drcrane/ledclock/esp8266terminal/londontzstruct.c

#include "tzstruct.h"

struct timezonechanges timezonechanges[] = 
{
{ 1521939600, 1540688400 }, // 2018
{ 1553994000, 1572138000 }, // 2019
{ 1585443600, 1603587600 }, // 2020
{ 1616893200, 1635642000 }, // 2021
{ 1648342800, 1667091600 }, // 2022
{ 1679792400, 1698541200 }, // 2023
{ 1711846800, 1729990800 }, // 2024
{ 1743296400, 1761440400 }, // 2025
{ 1774746000, 1792890000 }, // 2026
{ 1806195600, 1824944400 }, // 2027
{ 1837645200, 1856394000 }, // 2028
{ 1869094800, 1887843600 }, // 2029
{ 1901149200, 1919293200 }, // 2030
{ 1932598800, 1950742800 }, // 2031
{ 1964048400, 1982797200 }, // 2032
{ 1995498000, 2014246800 }, // 2033
{ 2026947600, 2045696400 }, // 2034
{ 0, 0 }
};
